gustii17/Projeto-8810/assets/partes/chave/circuito chave devounce.png

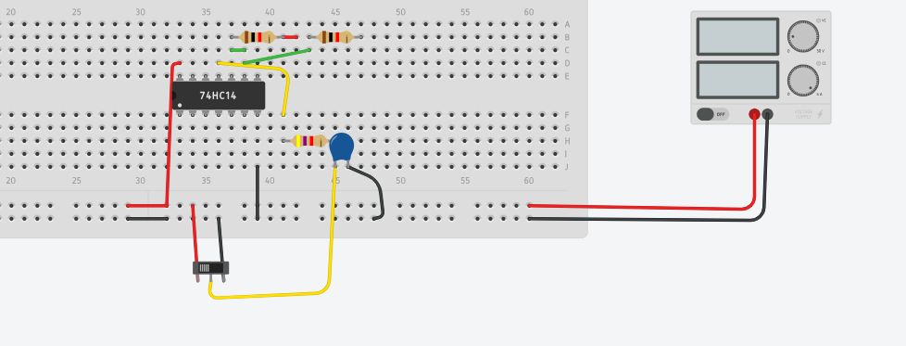
assets/partes/chave/circuito chave devounce.png
