gustii17/Projeto-8810/docs/datasheets/Captura de tela 2026-06-02 120615.png

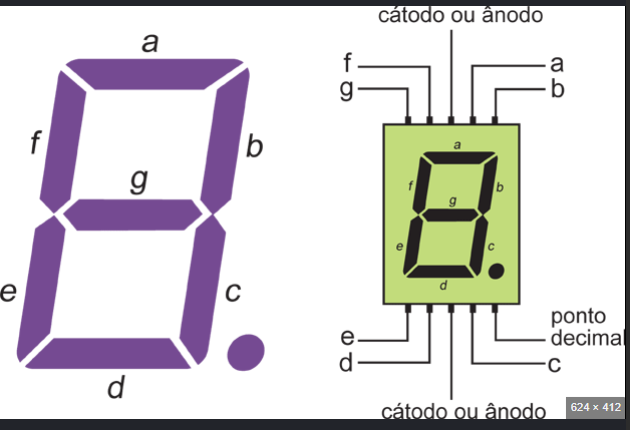
docs/datasheets/Captura de tela 2026-06-02 120615.png
