gustii17/Projeto-8810/docs/fotos/modulo 8810/acessorios da fonte.jpeg

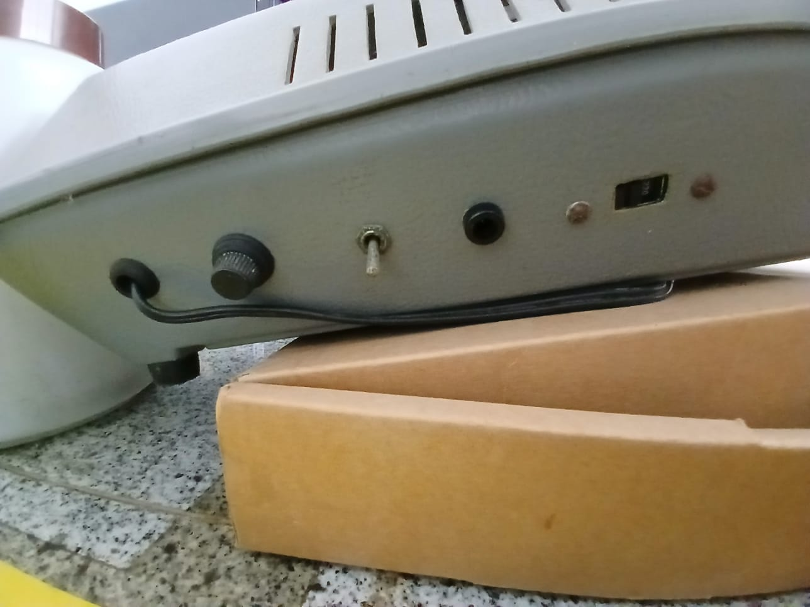
docs/fotos/modulo 8810/acessorios da fonte.jpeg
