gustii17/Projeto-8810/docs/fotos/modulo 8810/conexão.jpeg

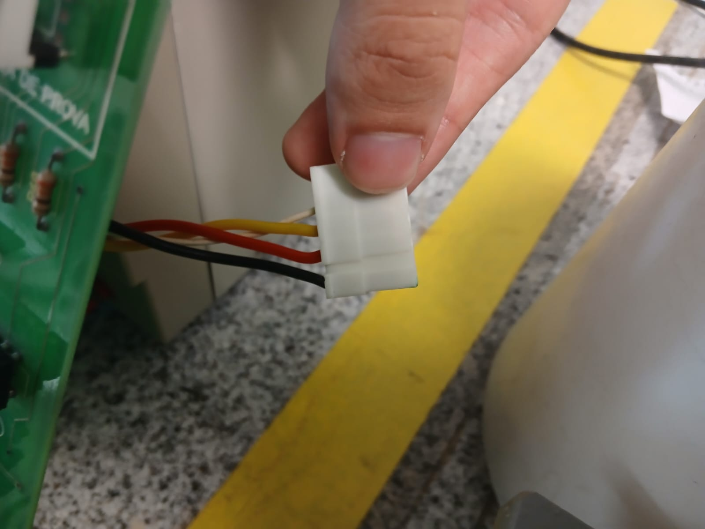
docs/fotos/modulo 8810/conexão.jpeg
