gustii17/Projeto-8810/docs/fotos/modulo 8810/placa baixo.jpeg

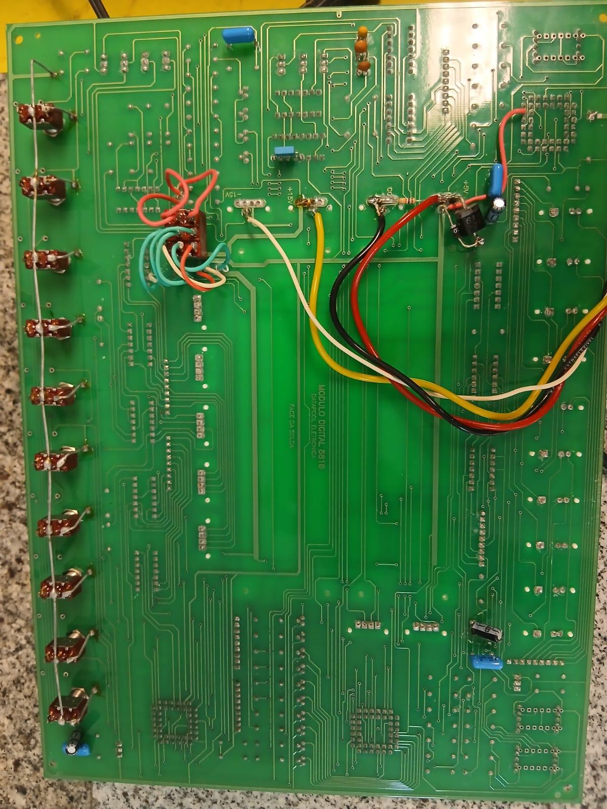
docs/fotos/modulo 8810/placa baixo.jpeg
