gustii17/Projeto-8810/docs/fotos/modulo 8810/placa de cima.jpeg

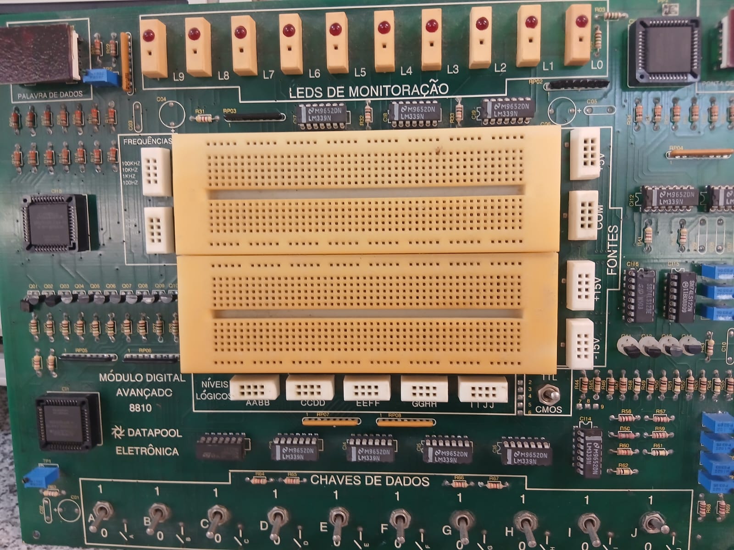
docs/fotos/modulo 8810/placa de cima.jpeg
