gustii17/Projeto-8810/docs/fotos/modulo 8810/transformador2.jpeg

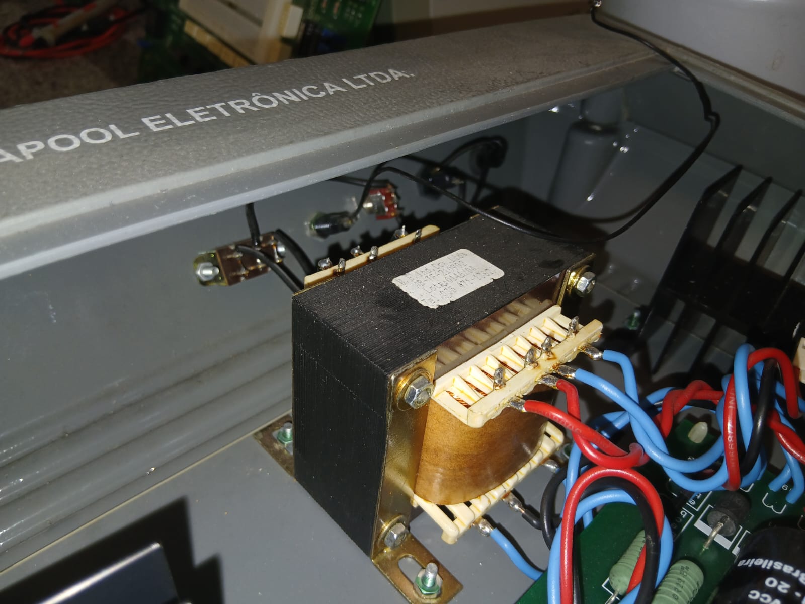
docs/fotos/modulo 8810/transformador2.jpeg
