gustii17/Projeto-8810/docs/fotos/transformador datapool 8410.png

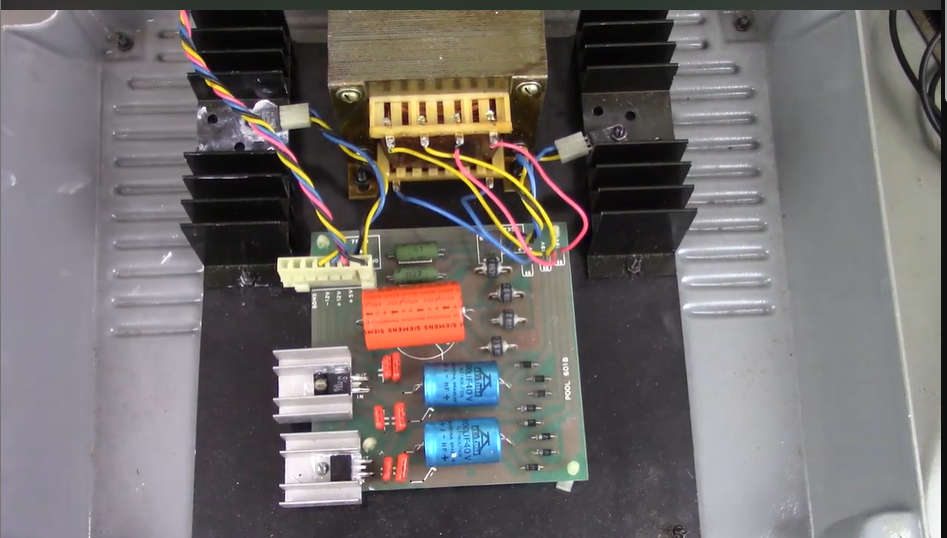
docs/fotos/transformador datapool 8410.png
