gustii17/Projeto-8810/schematics/logic-board/pcb/placa de cima/componentes/protoboard-de-830-puntos-1.snapshot.3/proto_830.png

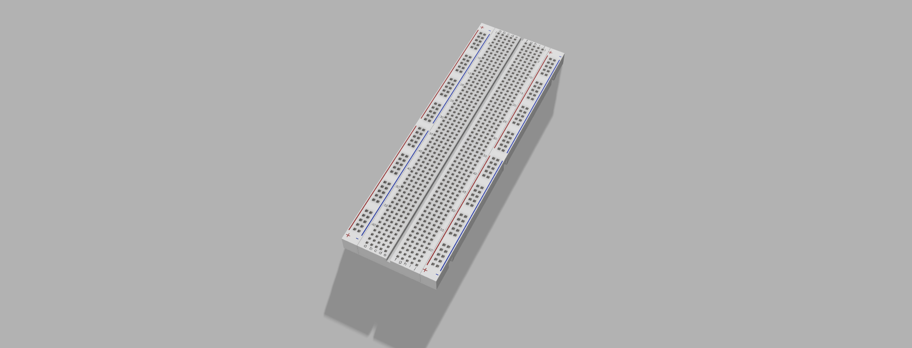
schematics/logic-board/pcb/placa de cima/componentes/protoboard-de-830-puntos-1.snapshot.3/proto_830.png
